ultrapalace/M0SS-101/images/image2.jpg

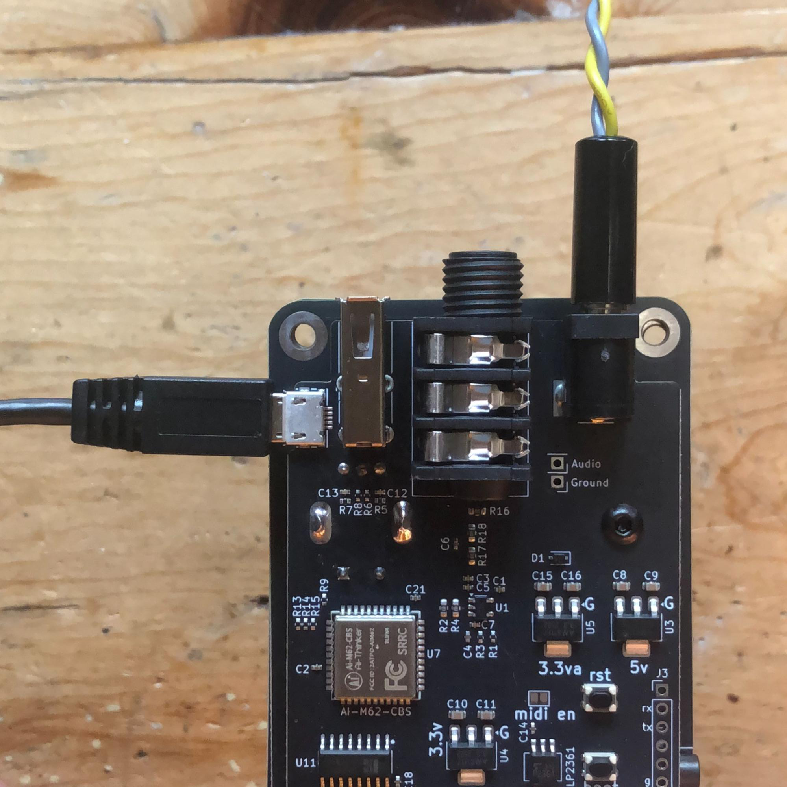
images/image2.jpg
