ultrapalace/M0SS-101/images/image4.png

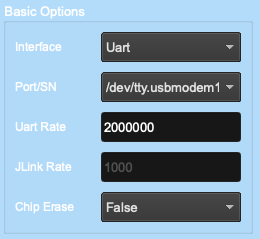
images/image4.png
