ultrapalace/M0SS-101/images/image10.png

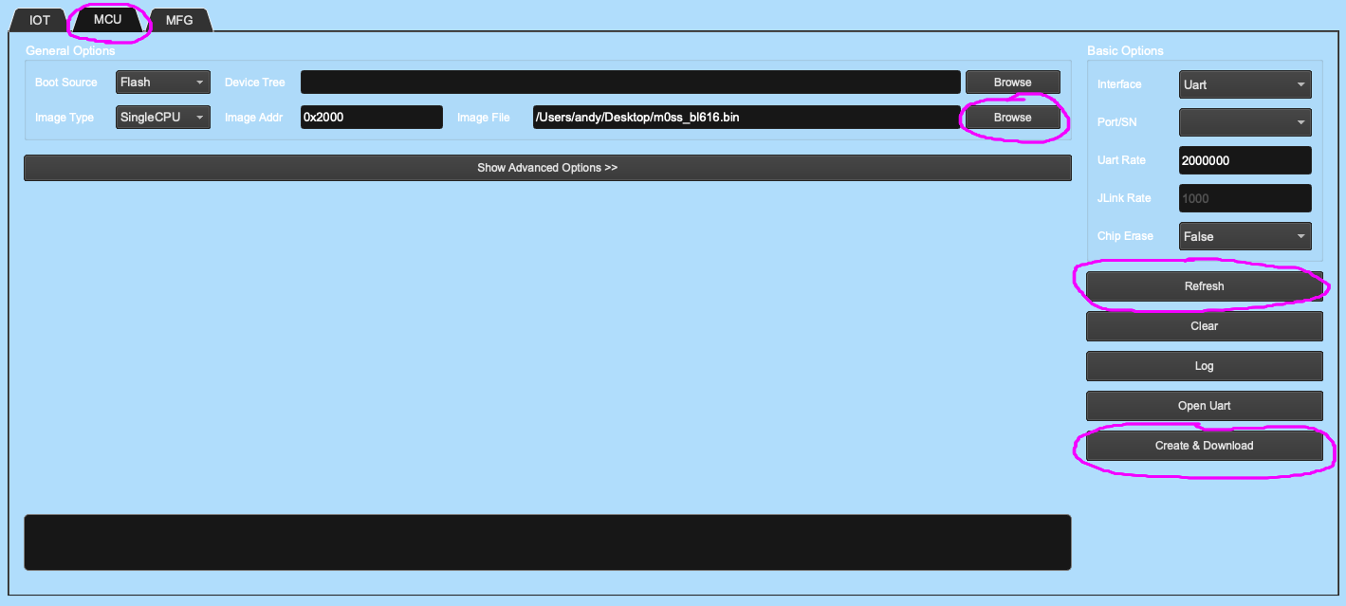
images/image10.png
