ultrapalace/M0SS-101/images/image25.png

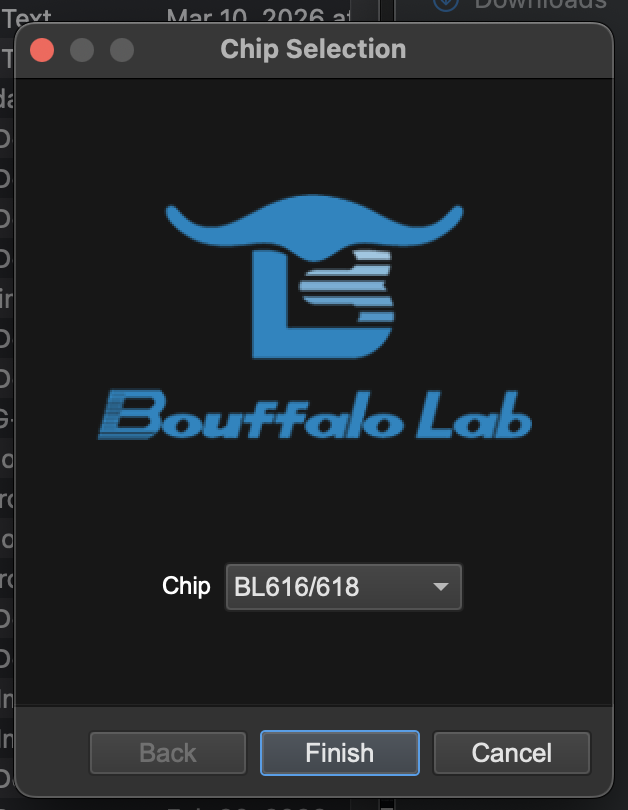
images/image25.png
