ultrapalace/M0SS-101/images/image26.png

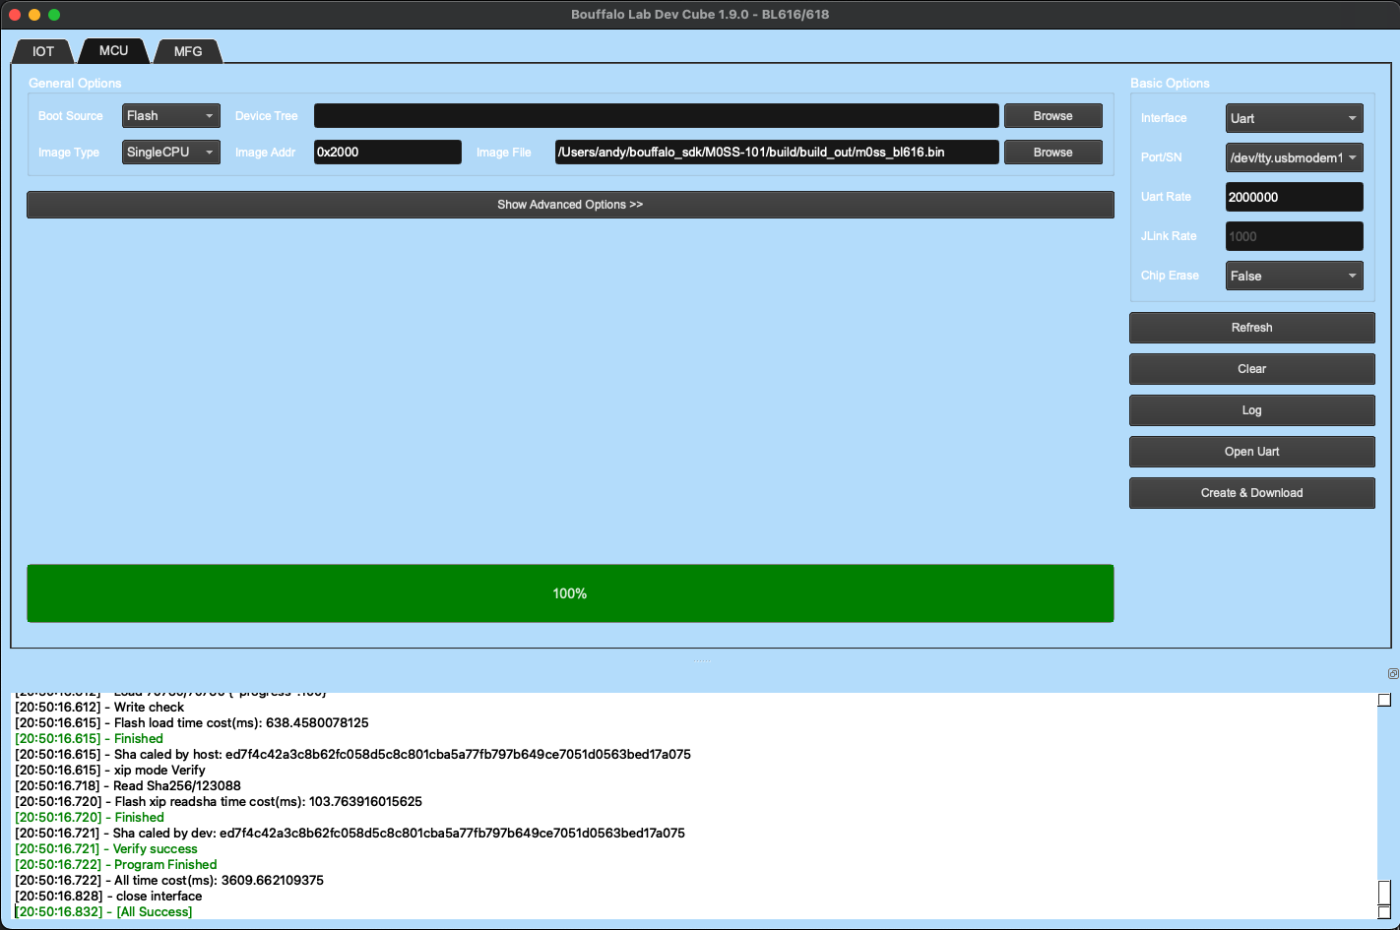
images/image26.png
